pepistrafforello/U3T/docs/article/images/rr_bottom.png

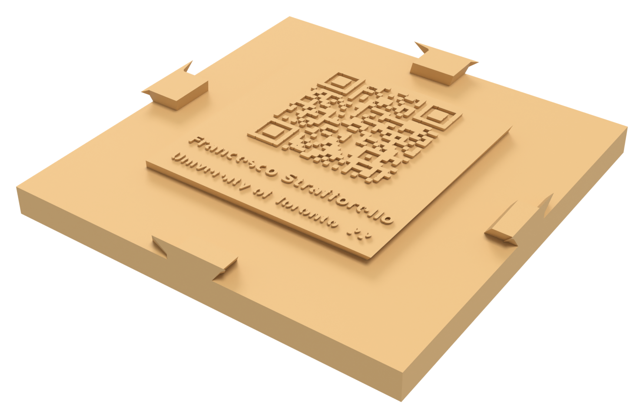
docs/article/images/rr_bottom.png
